werediver/current-dr-amp/LTspice/pot_lin.asc

R1: res; {Ra}
R2: res; {Rb}
Named nets: 1, 2, 3
.param Ra=R*(1-k)
.param Rb=R*k
